mhaack/halloween-pumpkin-fire/src/images.h

#define WiFi_Logo_width 60
#define WiFi_Logo_height 36
const char WiFi_Logo_bits[] PROGMEM = {
    0x00, 0x00, 0x00, 0x00, 0x00, 0x00, 0x00, 0x00, 0x00, 0x00, 0x00, 0xF8, 0x00, 0x00, 0x00, 0x00, 0x00, 0x00,
    0x80, 0xFF, 0x07, 0x00, 0x00, 0x00, 0x00, 0x00, 0xE0, 0xFF, 0x1F, 0x00, 0x00, 0x00, 0x00, 0x00, 0xF8, 0xFF,
    0x7F, 0x00, 0x00, 0x00, 0x00, 0x00, 0xFC, 0xFF, 0xFF, 0x00, 0x00, 0x00, 0x00, 0x00, 0xFE, 0xFF, 0xFF, 0x01,
    0x00, 0x00, 0x00, 0x00, 0xFF, 0xFF, 0xFF, 0x03, 0x00, 0x00, 0x00, 0xFC, 0xFF, 0xFF, 0xFF, 0xFF, 0x00, 0x00,
    0x00, 0xFF, 0xFF, 0xFF, 0x07, 0xC0, 0x83, 0x01, 0x80, 0xFF, 0xFF, 0xFF, 0x01, 0x00, 0x07, 0x00, 0xC0, 0xFF,
    0xFF, 0xFF, 0x00, 0x00, 0x0C, 0x00, 0xC0, 0xFF, 0xFF, 0x7C, 0x00, 0x60, 0x0C, 0x00, 0xC0, 0x31, 0x46, 0x7C,
    0xFC, 0x77, 0x08, 0x00, 0xE0, 0x23, 0xC6, 0x3C, 0xFC, 0x67, 0x18, 0x00, 0xE0, 0x23, 0xE4, 0x3F, 0x1C, 0x00,
    0x18, 0x00, 0xE0, 0x23, 0x60, 0x3C, 0x1C, 0x70, 0x18, 0x00, 0xE0, 0x03, 0x60, 0x3C, 0x1C, 0x70, 0x18, 0x00,
    0xE0, 0x07, 0x60, 0x3C, 0xFC, 0x73, 0x18, 0x00, 0xE0, 0x87, 0x70, 0x3C, 0xFC, 0x73, 0x18, 0x00, 0xE0, 0x87,
    0x70, 0x3C, 0x1C, 0x70, 0x18, 0x00, 0xE0, 0x87, 0x70, 0x3C, 0x1C, 0x70, 0x18, 0x00, 0xE0, 0x8F, 0x71, 0x3C,
    0x1C, 0x70, 0x18, 0x00, 0xC0, 0xFF, 0xFF, 0x3F, 0x00, 0x00, 0x08, 0x00, 0xC0, 0xFF, 0xFF, 0x1F, 0x00, 0x00,
    0x0C, 0x00, 0x80, 0xFF, 0xFF, 0x1F, 0x00, 0x00, 0x06, 0x00, 0x80, 0xFF, 0xFF, 0x0F, 0x00, 0x00, 0x07, 0x00,
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
    0x36, 0x0C, 0x07, 0x00, 0x33, 0x18, 0x03, 0xC0, 0x19, 0x30, 0x07, 0xE0, 0x0C, 0x60, 0x7C, 0x3E, 0x06, 0xC0, 0xF1,
    0x8F, 0x03, 0x80, 0x03, 0xE0, 0x01, 0x00, 0x7E, 0x7D, 0x00, 0x00, 0xF0, 0x0F, 0x00,
};

#define fire_width 24
#define fire_height 32
static unsigned char fire_bits[] = {
    0x00, 0xC0, 0x00, 0x00, 0xE0, 0x00, 0x00, 0xF0, 0x00, 0x00, 0xB8, 0x01, 0x00, 0x98, 0x01, 0x00,
    0x0C, 0x03, 0x00, 0x0C, 0x07, 0x00, 0x06, 0x06, 0x00, 0x06, 0x0C, 0x00, 0x03, 0x0C, 0x00, 0x03,
    0x18, 0x18, 0x03, 0x30, 0x1C, 0x03, 0x30, 0x36, 0x03, 0x60, 0x36, 0x03, 0x60, 0xE3, 0x03, 0xC0,
    0xC3, 0x03, 0xC0, 0x03, 0x21, 0xC0, 0x03, 0x30, 0xC0, 0x03, 0x78, 0xC0, 0x03, 0x78, 0xC0, 0x03,
    0xCC, 0xC0, 0x03, 0xCF, 0xC0, 0x83, 0x8F, 0xC1, 0x86, 0x8F, 0x61, 0xC6, 0x86, 0x63, 0x8C, 0x00,
    0x33, 0x98, 0x00, 0x19, 0xB8, 0x81, 0x1D, 0xF0, 0xC3, 0x0F, 0xC0, 0xFF, 0x03, 0x00, 0xFF, 0x00,
};
